DreaM117er/Paicorea/file/datasheet/RP2040 Core-A datasheet.jpg

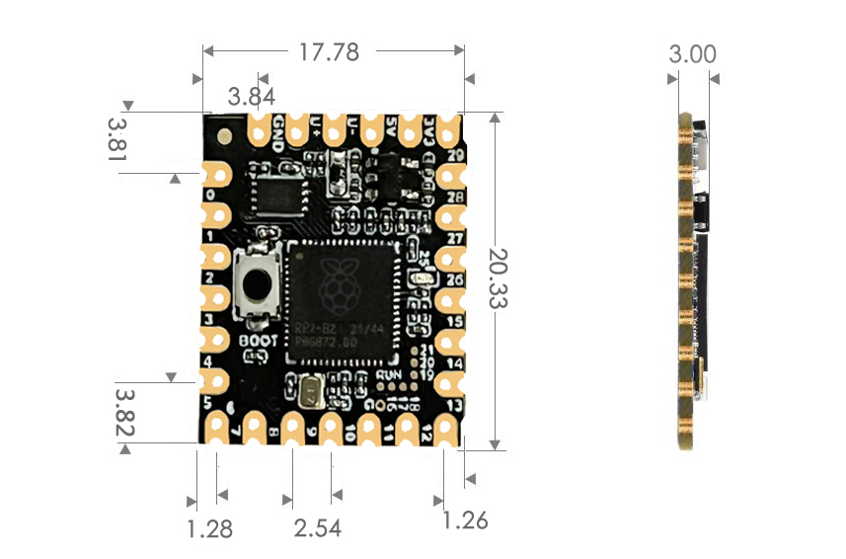
file/datasheet/RP2040 Core-A datasheet.jpg
