DreaM117er/Paicorea/file/datasheet/RP2040 Core-A-1.png

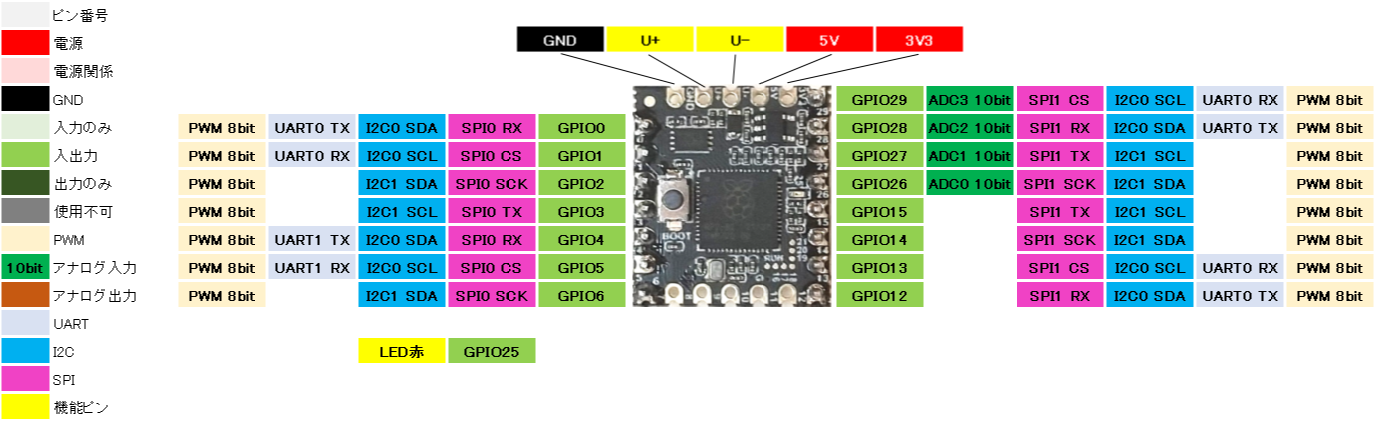
file/datasheet/RP2040 Core-A-1.png
