DreaM117er/Paicorea/file/datasheet/RP2040 Core-A-2.png

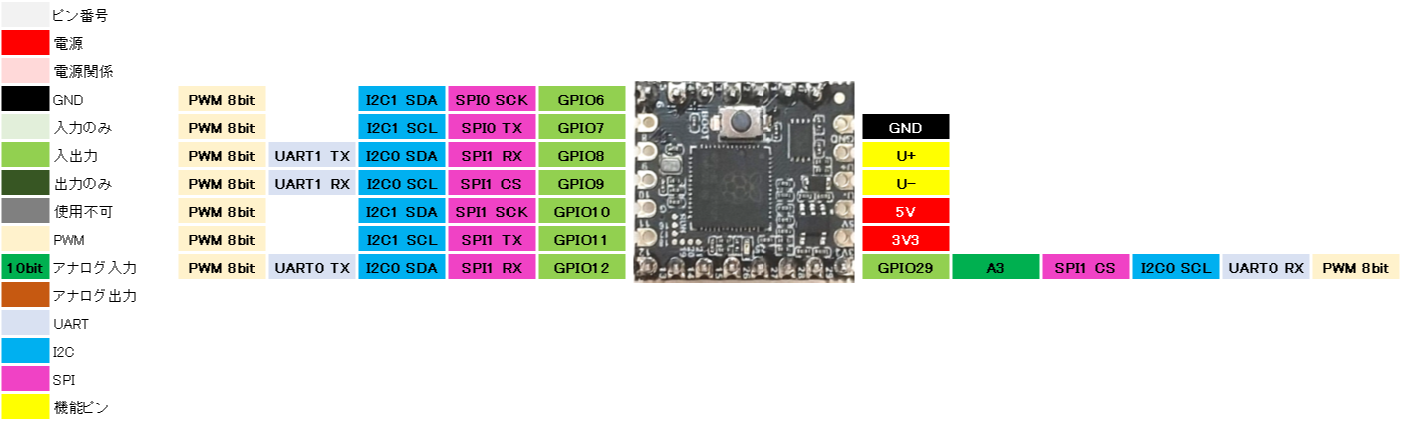
file/datasheet/RP2040 Core-A-2.png
