DreaM117er/Paicorea/file/Layout.png

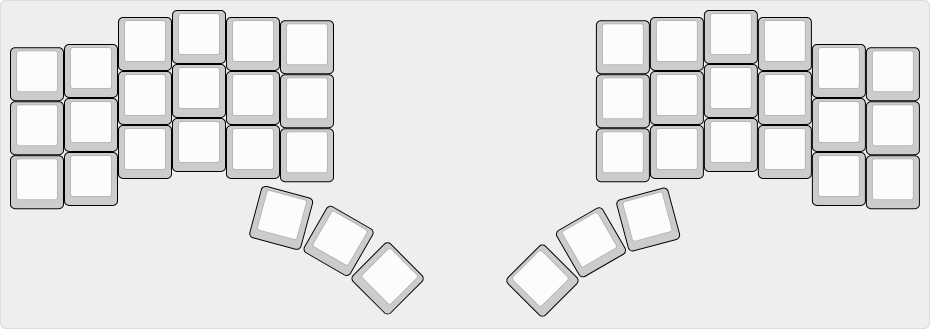
file/Layout.png
