DreaM117er/Paicorea/pic/pic5.jpg

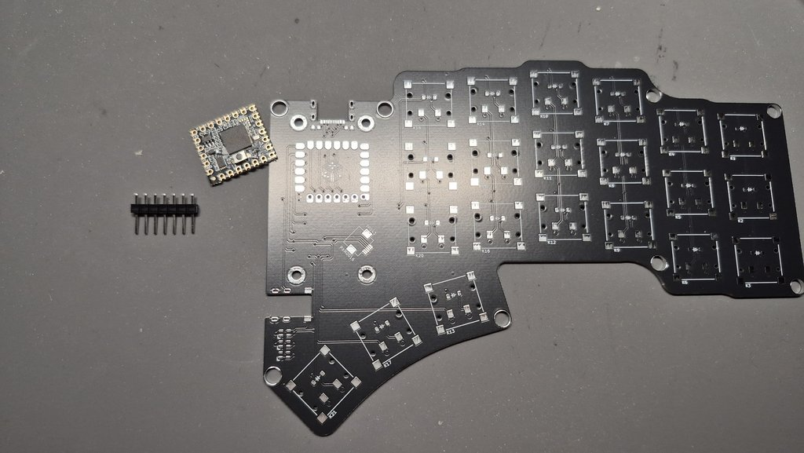
pic/pic5.jpg
