DreaM117er/Paicorea/pic/pic6.jpg

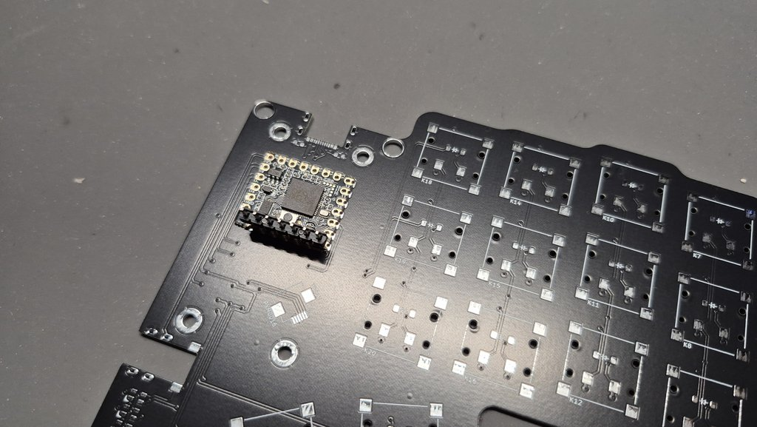
pic/pic6.jpg
