DreaM117er/Paicorea/pic/pic7.jpg

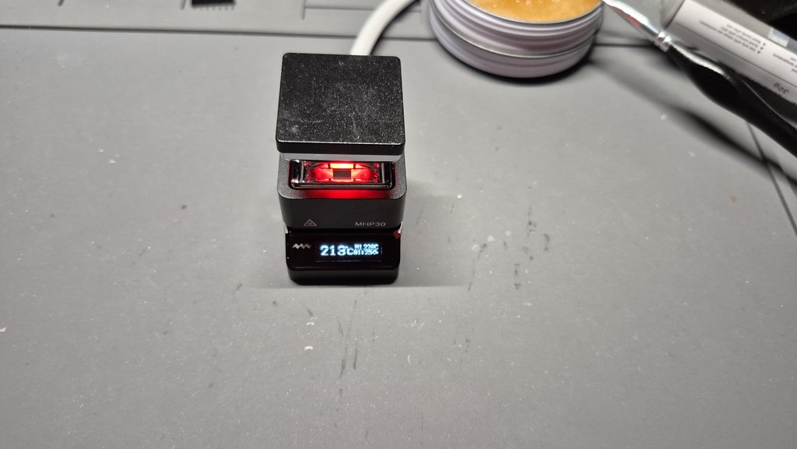
pic/pic7.jpg
